Atackator/InkTime_TSC/Images/image1.png

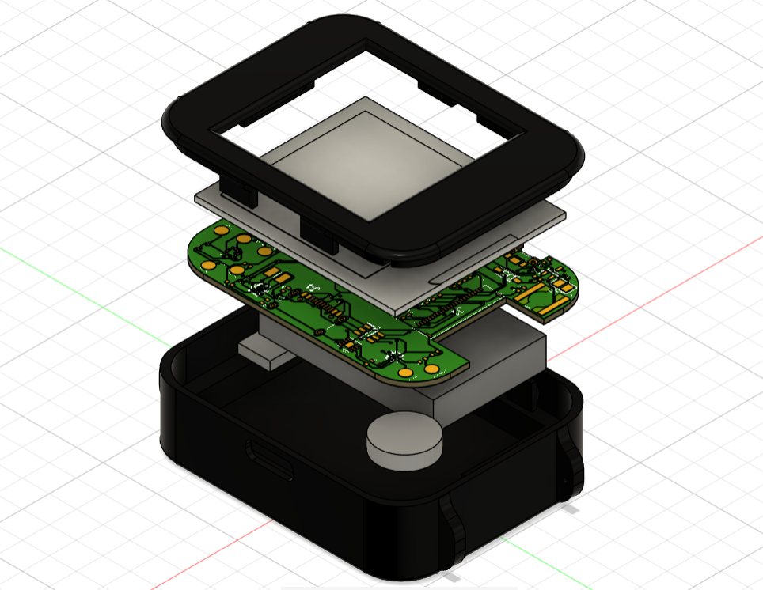
Images/image1.png
