Atackator/InkTime_TSC/Images/image2.png

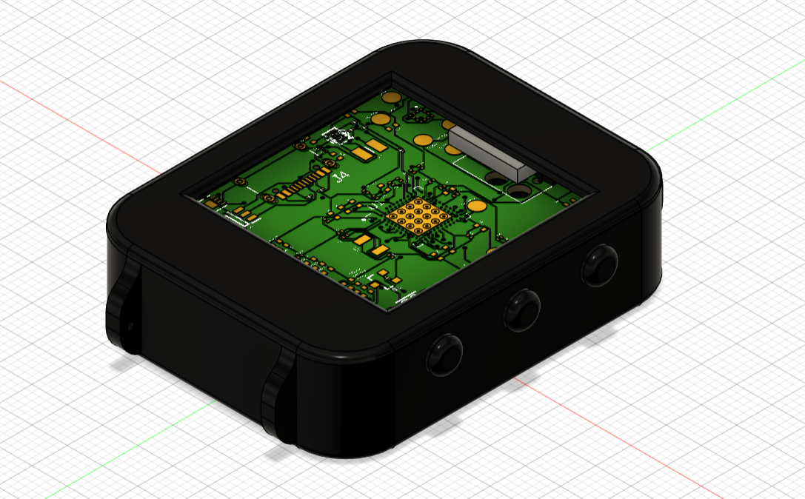
Images/image2.png
