Atackator/InkTime_TSC/Images/image3.png

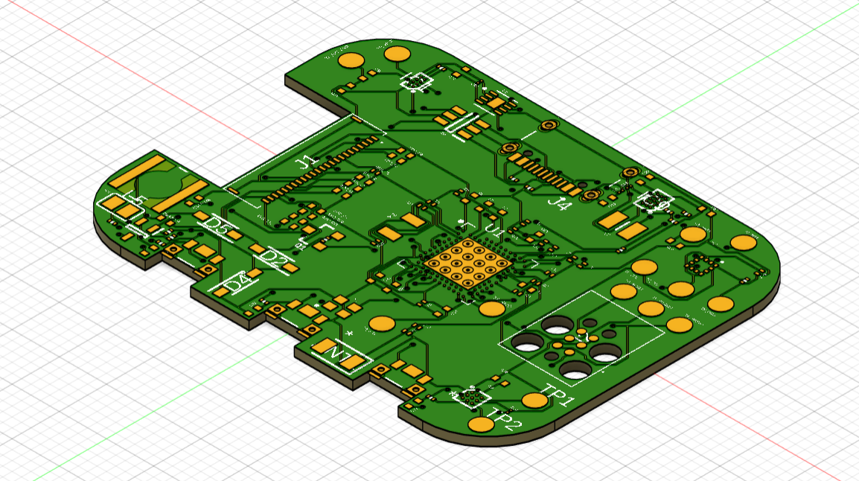
Images/image3.png
