Atackator/InkTime_TSC/Images/image4.png

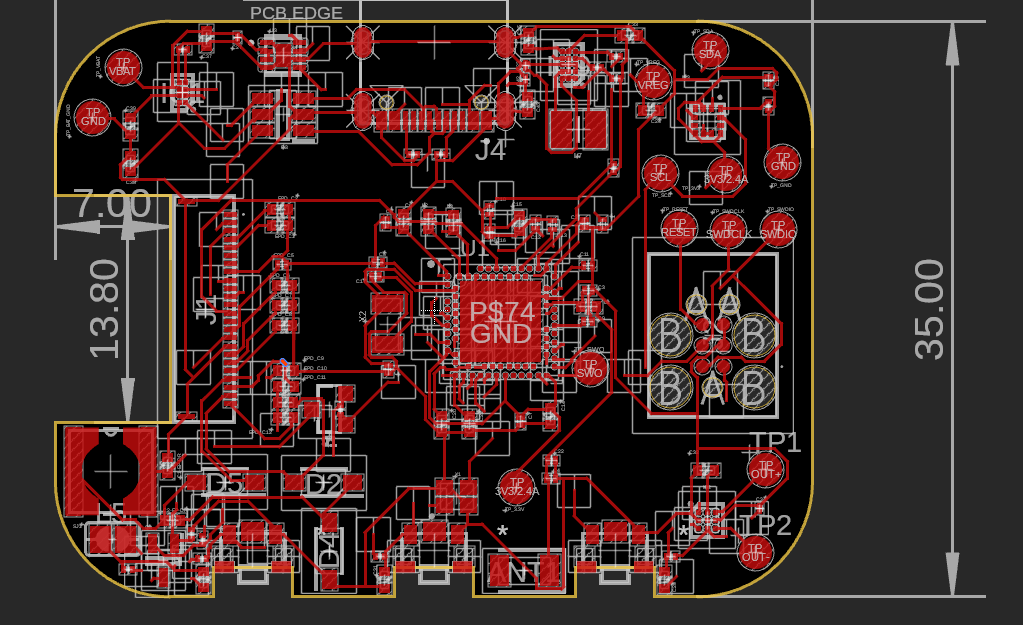
Images/image4.png
