Atackator/InkTime_TSC/Images/image5.png

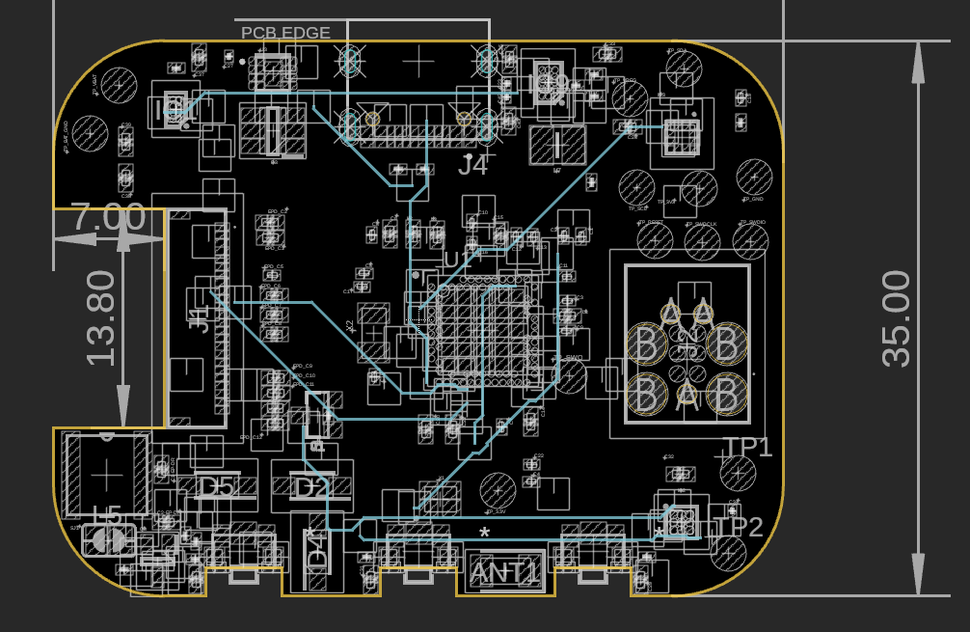
Images/image5.png
