Atackator/InkTime_TSC/Images/image6.png

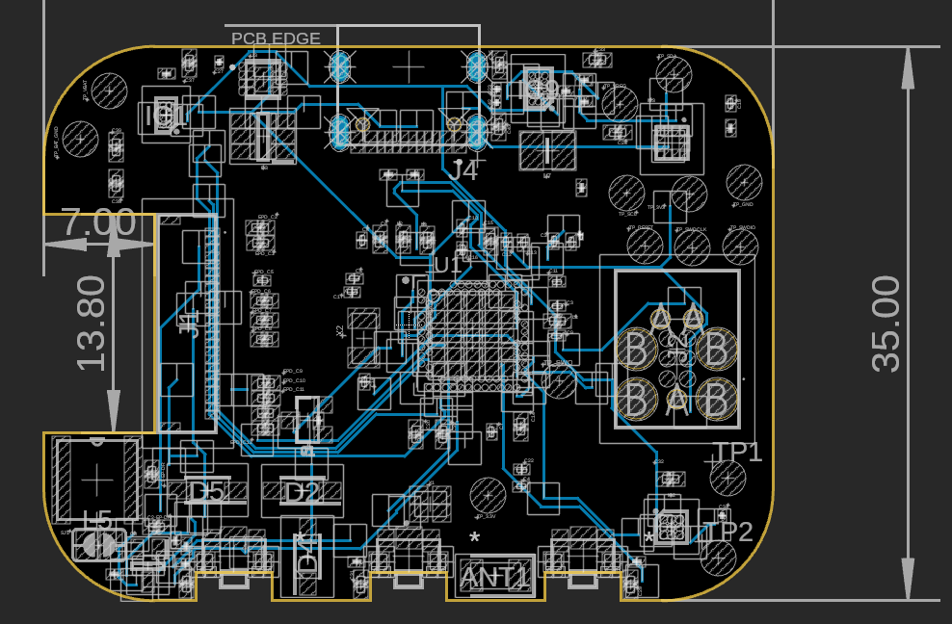
Images/image6.png
